halilibrahimcetin/IoTbasedfiretruck/3D ARABA/_0.jpg

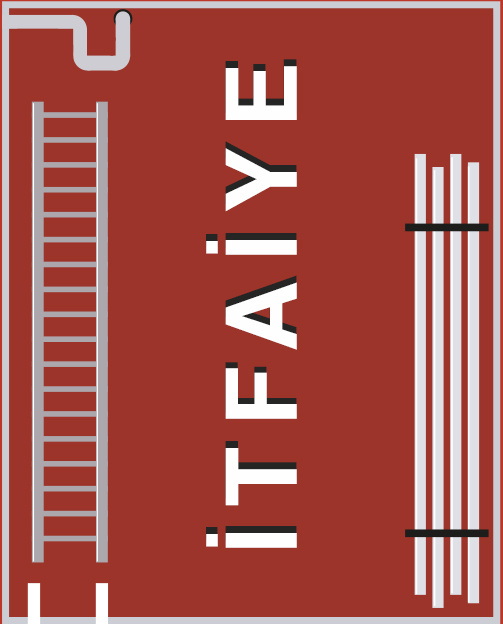
3D ARABA/_0.jpg
