halilibrahimcetin/IoTbasedfiretruck/3D ARABA/arka22.jpg

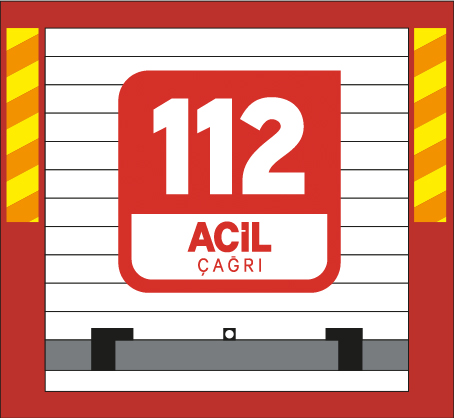
3D ARABA/arka22.jpg
