halilibrahimcetin/IoTbasedfiretruck/3D ARABA/sollike.jpg

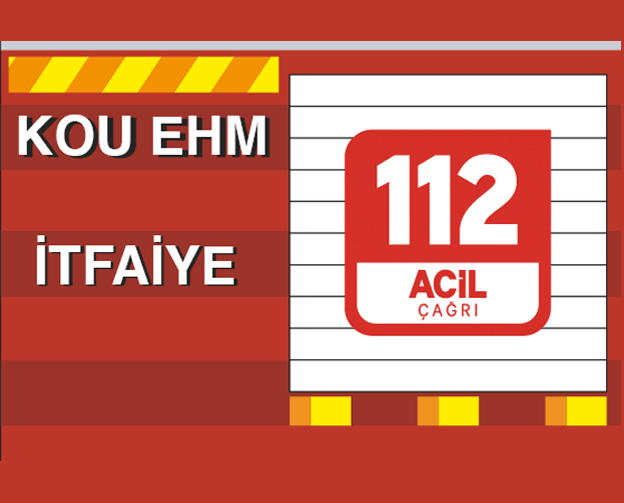
3D ARABA/sollike.jpg
