halilibrahimcetin/IoTbasedfiretruck/3D ARABA/sollke.jpg

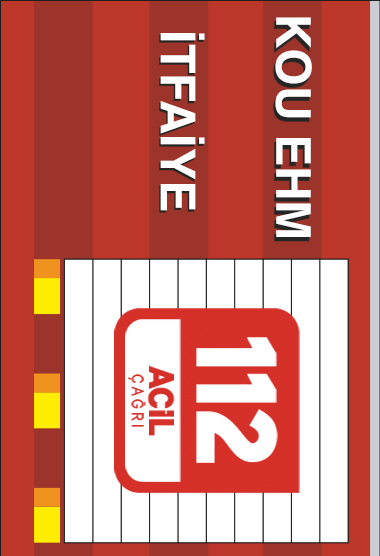
3D ARABA/sollke.jpg
