halilibrahimcetin/IoTbasedfiretruck/3d/STL/microservostand.stl

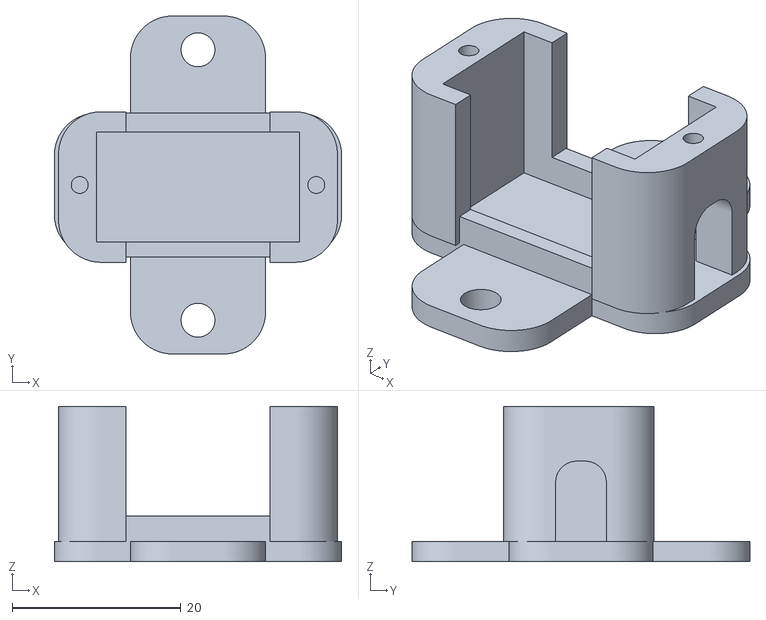
[picture p75: CAD file, 2025-07-01]
3d/STL/microservostand.stl
34.0 x 40.0 x 18.4
