halilibrahimcetin/IoTbasedfiretruck/3d/STL/v5_lid.stl

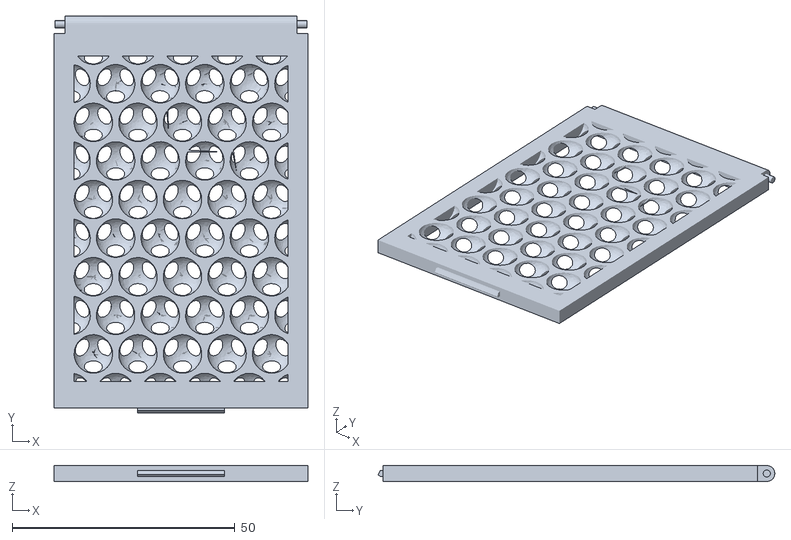
[picture p76: CAD file, 2025-07-01]
3d/STL/v5_lid.stl
57.0 x 89.0 x 3.61
