halilibrahimcetin/IoTbasedfiretruck/3d/3lü4mm.SLDPRT

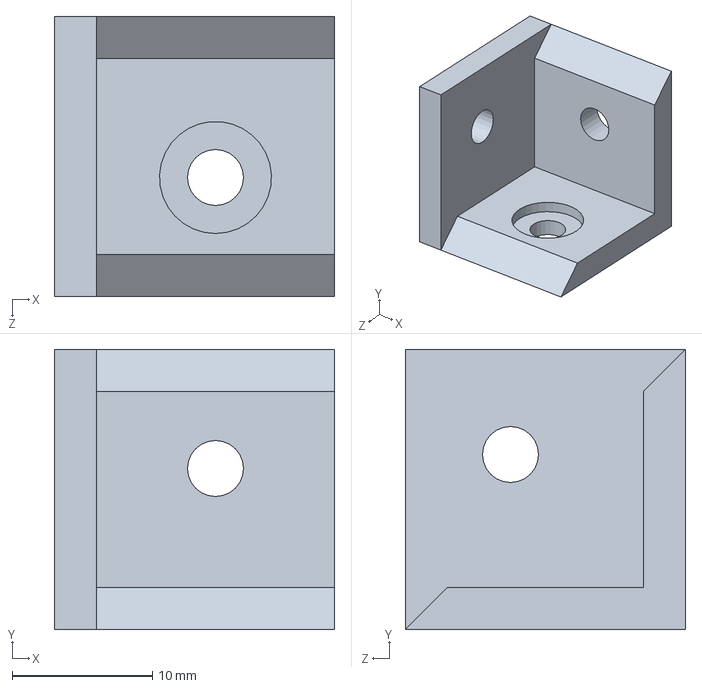
[picture p77: CAD file, 2025-07-01]
3d/3lü4mm.SLDPRT
20.0 x 20.0 x 20.0 mm
