halilibrahimcetin/IoTbasedfiretruck/3d/piltutucu.SLDPRT

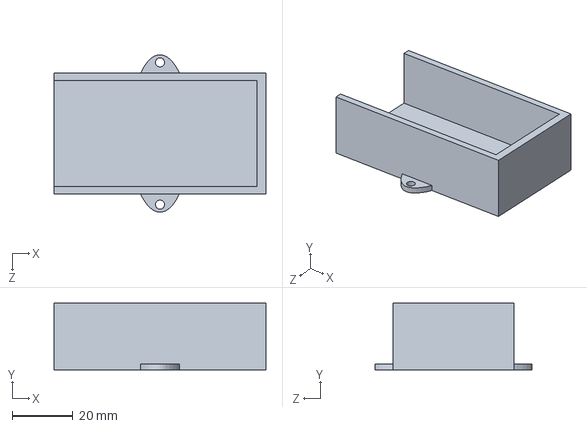
[picture p78: CAD file, 2025-07-01]
3d/piltutucu.SLDPRT
70.0 x 22.0 x 52.0 mm
