halilibrahimcetin/IoTbasedfiretruck/3d/kapak.SLDPRT

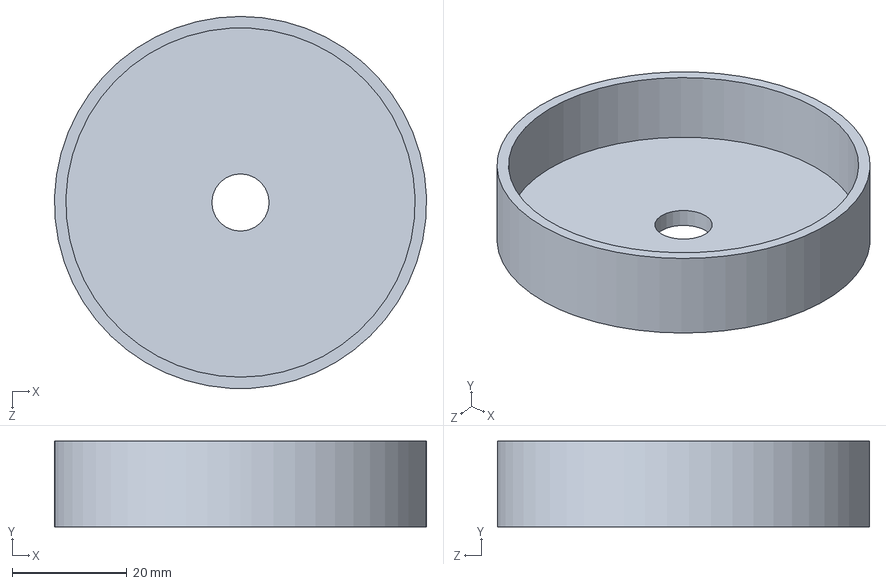
[picture p79: CAD file, 2025-07-01]
3d/kapak.SLDPRT
65.0 x 15.0 x 65.0 mm
